thinklearndo/garagedooropennotifier/images/capacitor_negative.jpg

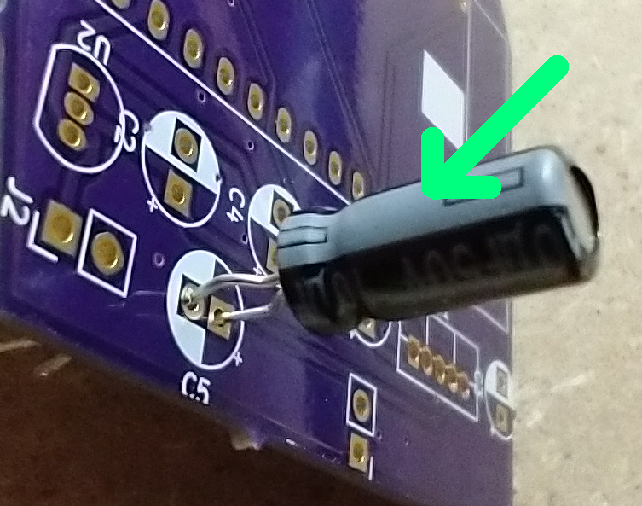
images/capacitor_negative.jpg
