thinklearndo/garagedooropennotifier/images/capacitor_positive.jpg

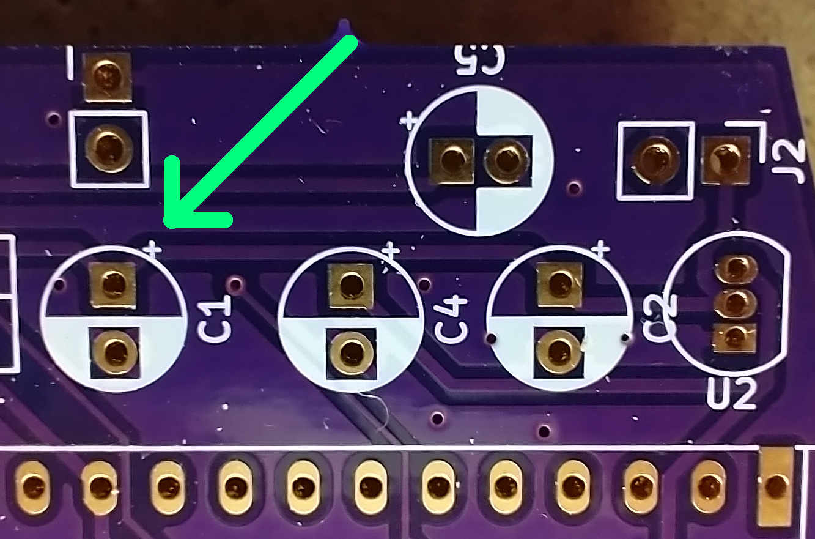
images/capacitor_positive.jpg
