thinklearndo/garagedooropennotifier/images/mounted.jpg

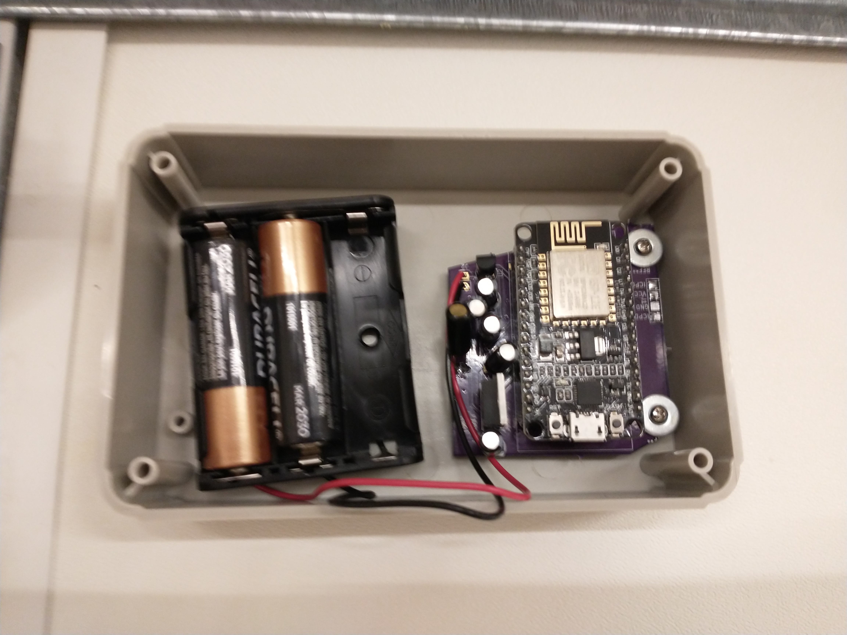
images/mounted.jpg
