thinklearndo/garagedooropennotifier/images/negative_gnd_probe.jpg

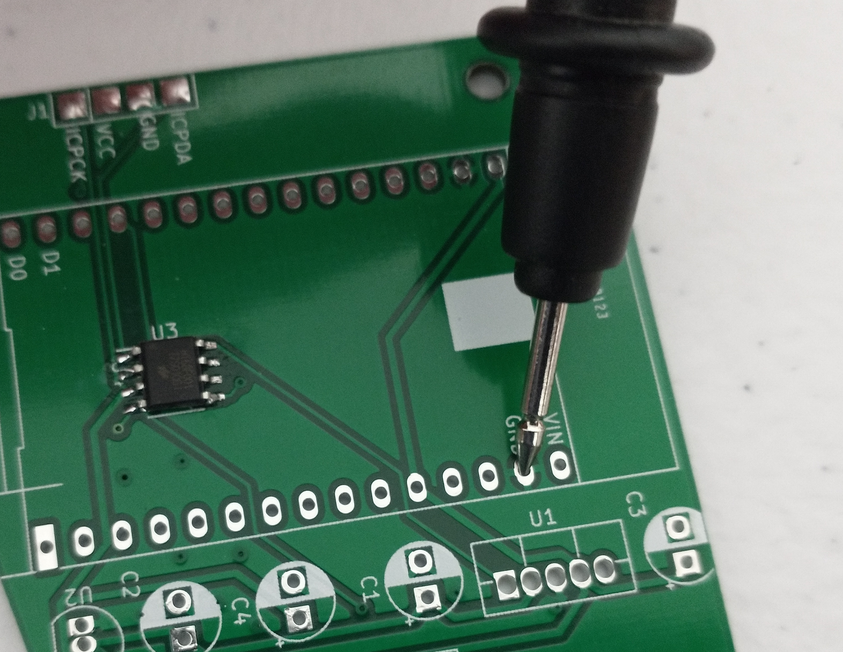
images/negative_gnd_probe.jpg
