thinklearndo/garagedooropennotifier/images/power_orientation.jpg

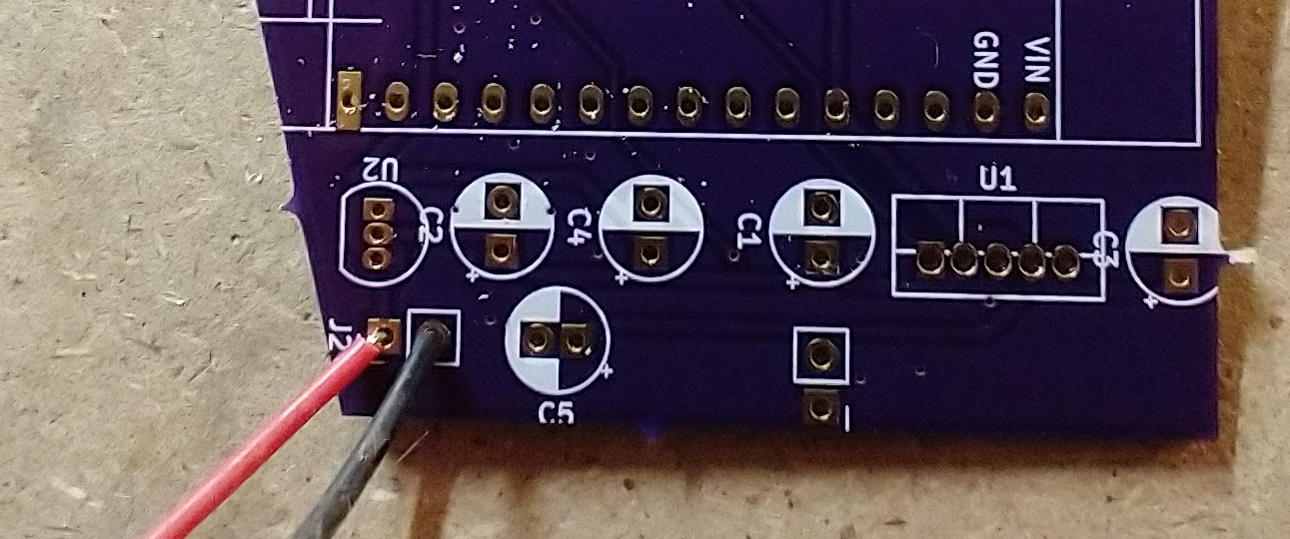
images/power_orientation.jpg
