thinklearndo/garagedooropennotifier/images/power_orientation_fixed.jpg

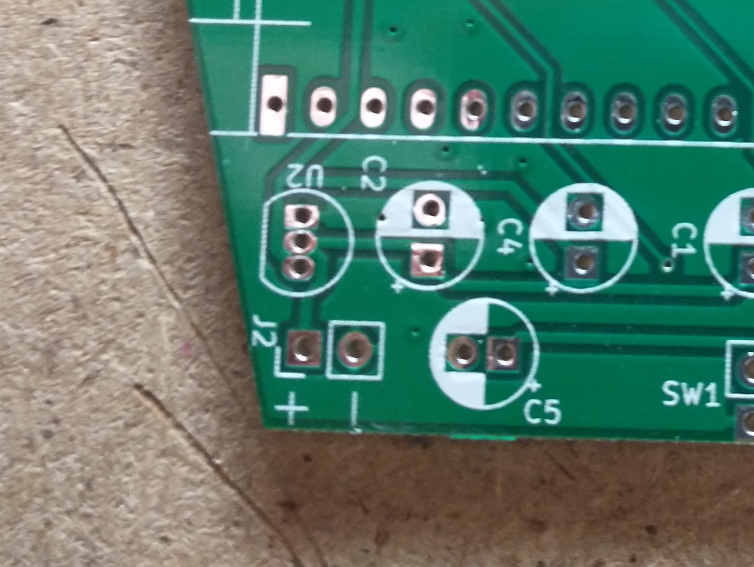
images/power_orientation_fixed.jpg
