thinklearndo/garagedooropennotifier/images/screw_washer.jpg

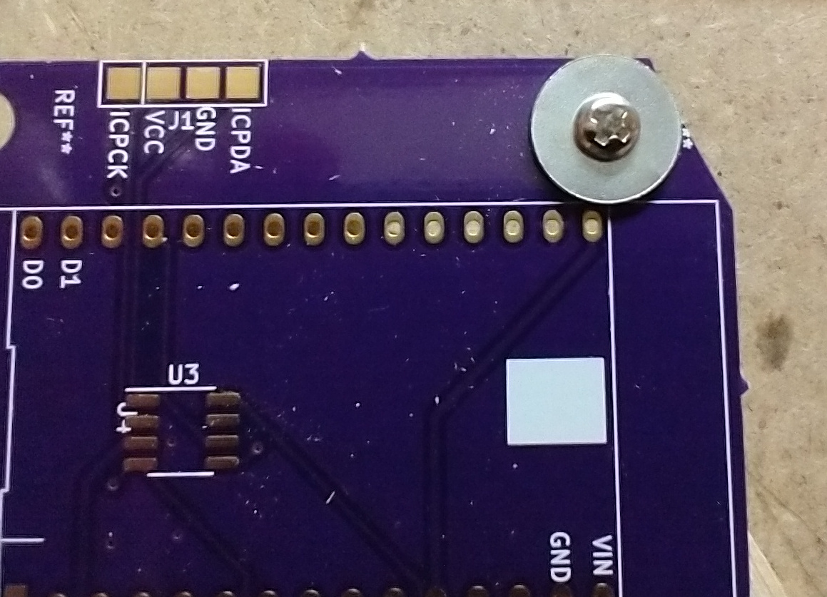
images/screw_washer.jpg
