thinklearndo/garagedooropennotifier/images/U1_orientation.jpg

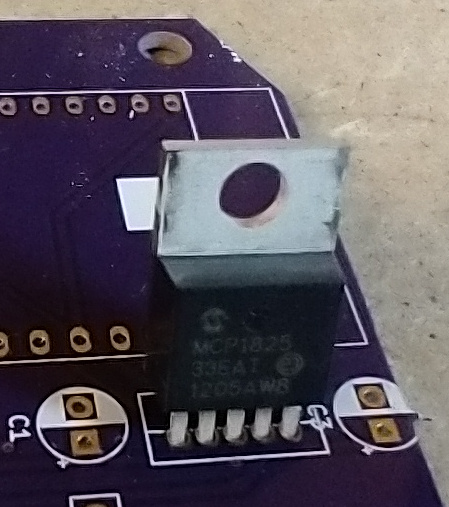
images/U1_orientation.jpg
