thinklearndo/garagedooropennotifier/images/U2_orientation.jpg

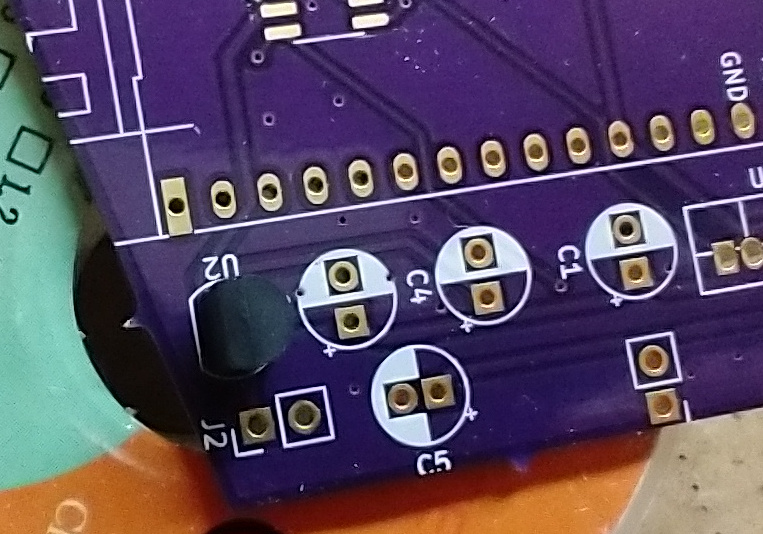
images/U2_orientation.jpg
