thinklearndo/garagedooropennotifier/images/headers_installed.jpg

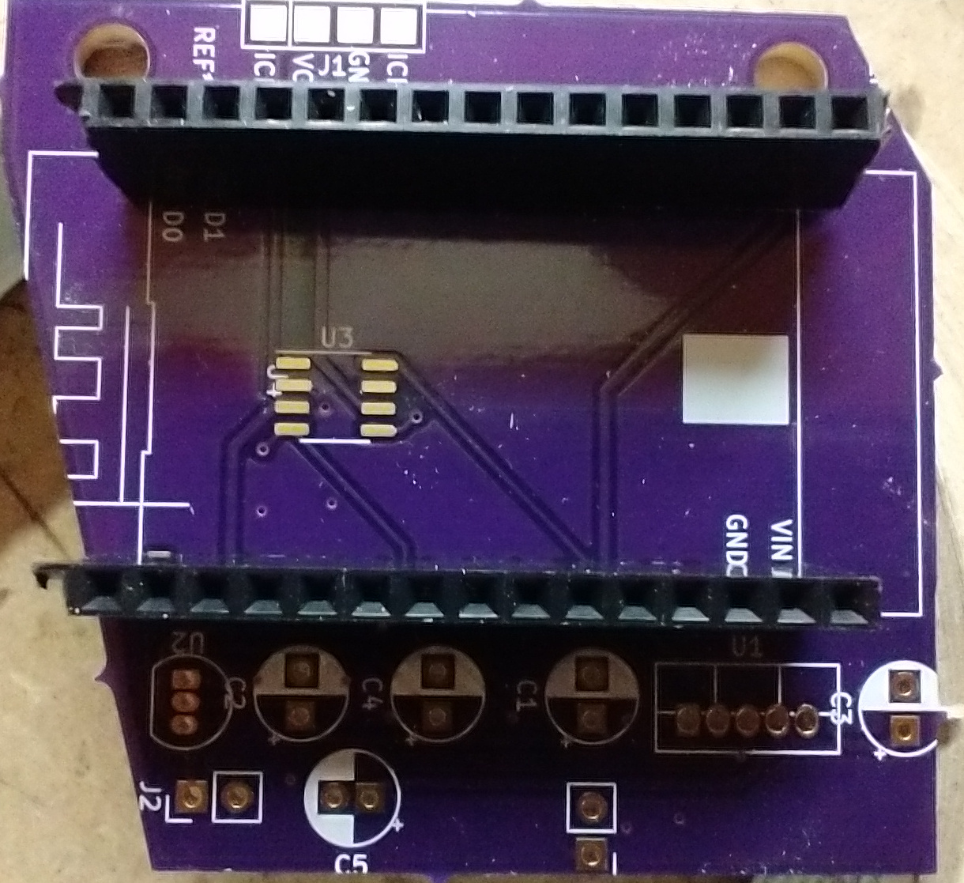
images/headers_installed.jpg
